LieBtrau/garage-door-rke/hardware/testReports/measurementResults/BRD220522_2/4.1Vin_default_tx_power.png

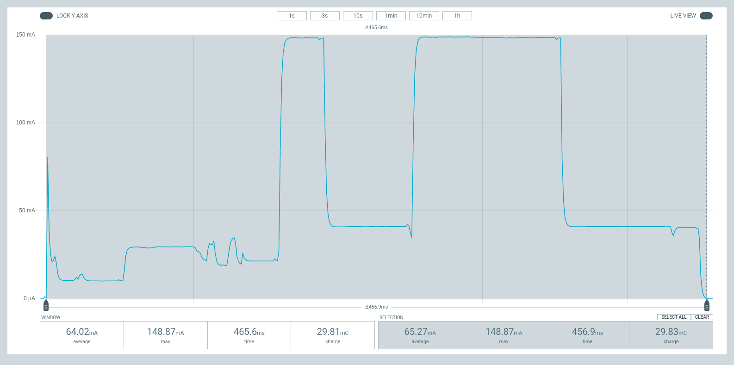
hardware/testReports/measurementResults/BRD220522_2/4.1Vin_default_tx_power.png
