LieBtrau/garage-door-rke/hardware/testReports/measurementResults/BRD220522_2/SPI/IMG_20221129_220042_032.jpg

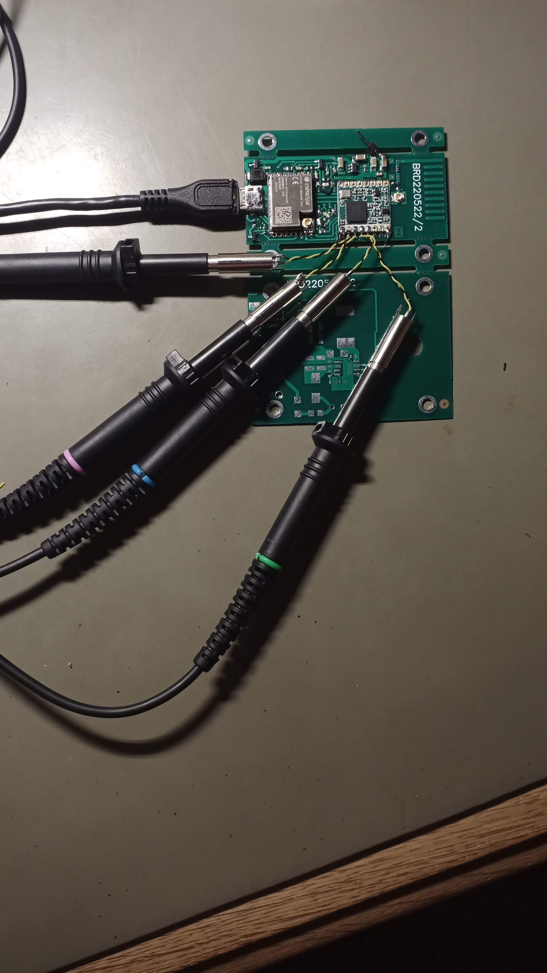
hardware/testReports/measurementResults/BRD220522_2/SPI/IMG_20221129_220042_032.jpg
