LieBtrau/garage-door-rke/hardware/testReports/measurementResults/BRD220522_2/SPI/MISO_timing.png

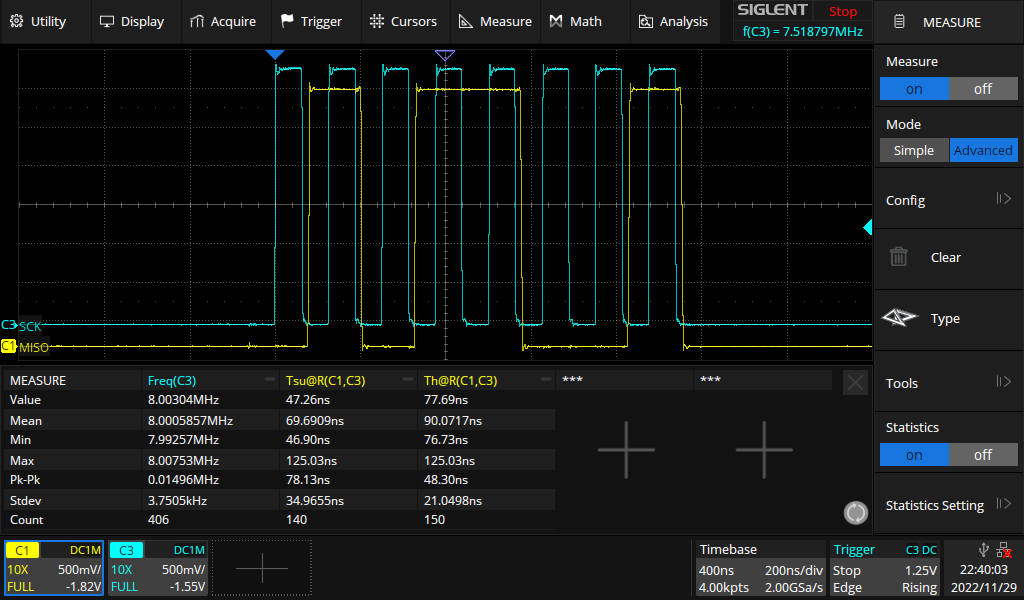
hardware/testReports/measurementResults/BRD220522_2/SPI/MISO_timing.png
