LieBtrau/garage-door-rke/hardware/testReports/measurementResults/BRD220522_2/SPI/MOSI.png

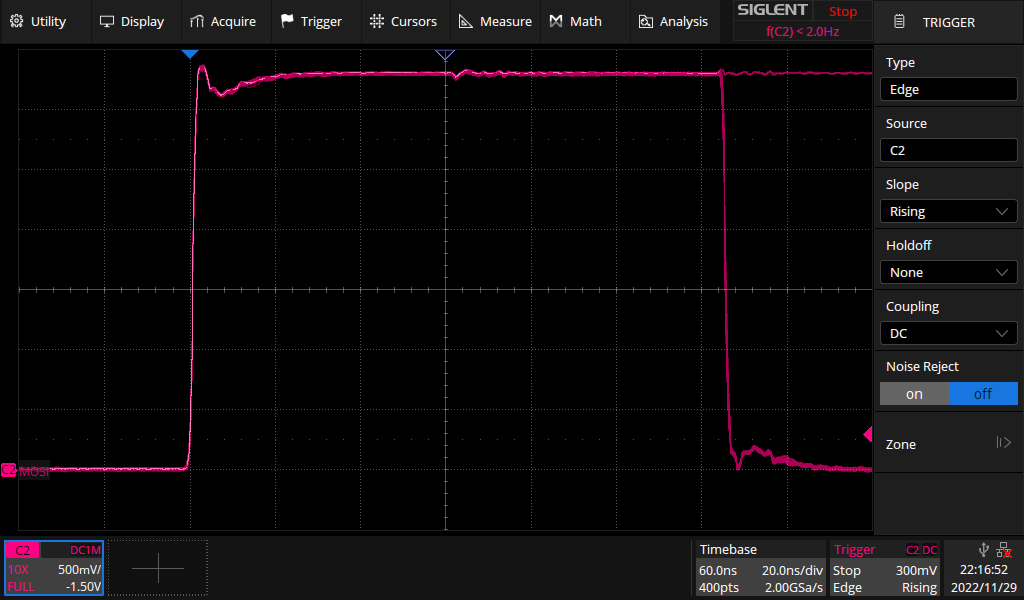
hardware/testReports/measurementResults/BRD220522_2/SPI/MOSI.png
