LieBtrau/garage-door-rke/hardware/testReports/measurementResults/BRD220522_2/SPI/nCS_fallingEdge.png

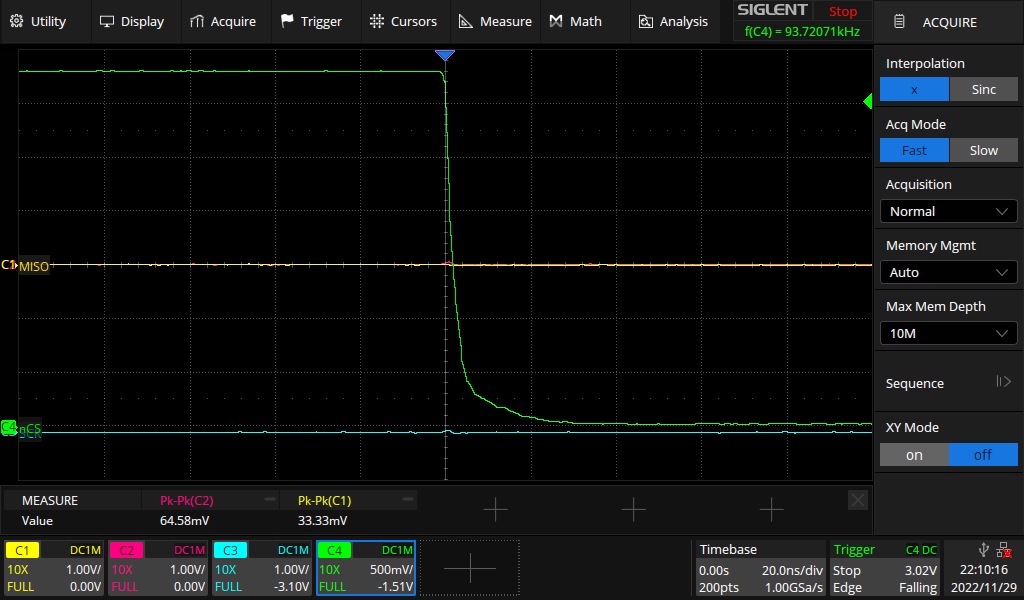
hardware/testReports/measurementResults/BRD220522_2/SPI/nCS_fallingEdge.png
