LieBtrau/garage-door-rke/hardware/testReports/measurementResults/BRD220522_2/SPI/SCK.png

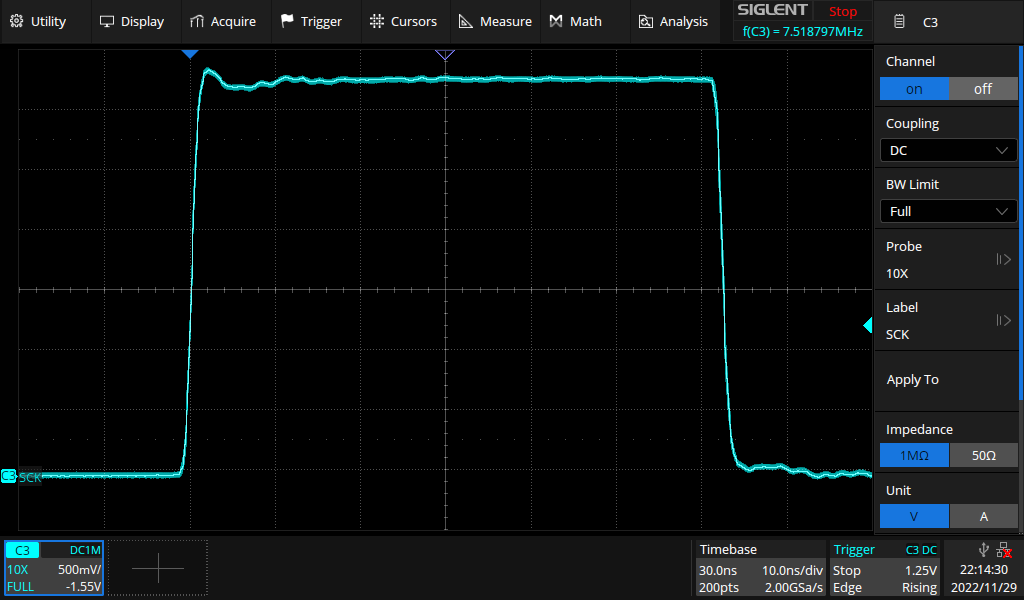
hardware/testReports/measurementResults/BRD220522_2/SPI/SCK.png
