LieBtrau/garage-door-rke/hardware/testReports/measurementResults/BRD220523_1/5V_rampUp.png

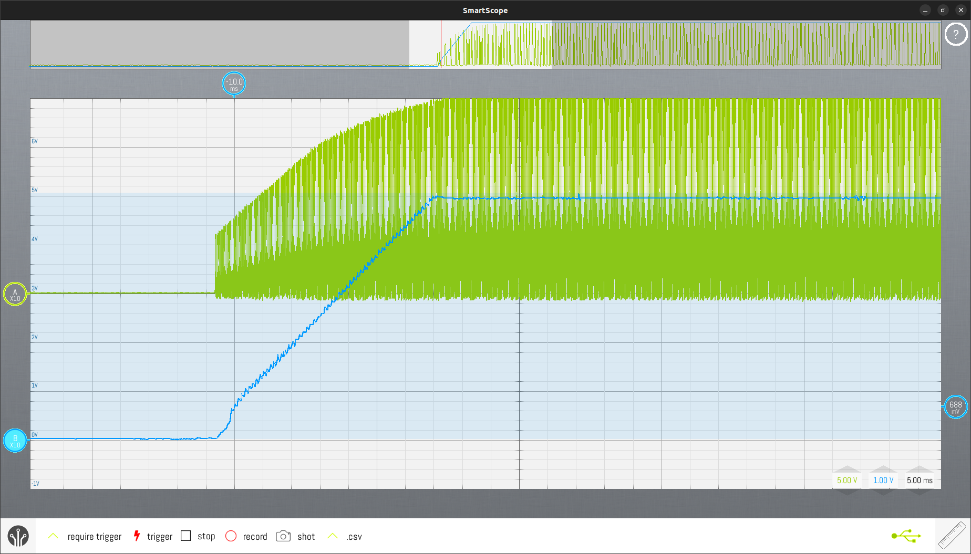
hardware/testReports/measurementResults/BRD220523_1/5V_rampUp.png
