LieBtrau/garage-door-rke/hardware/testReports/measurementResults/BRD220523_1/10Vin_1Aout.png

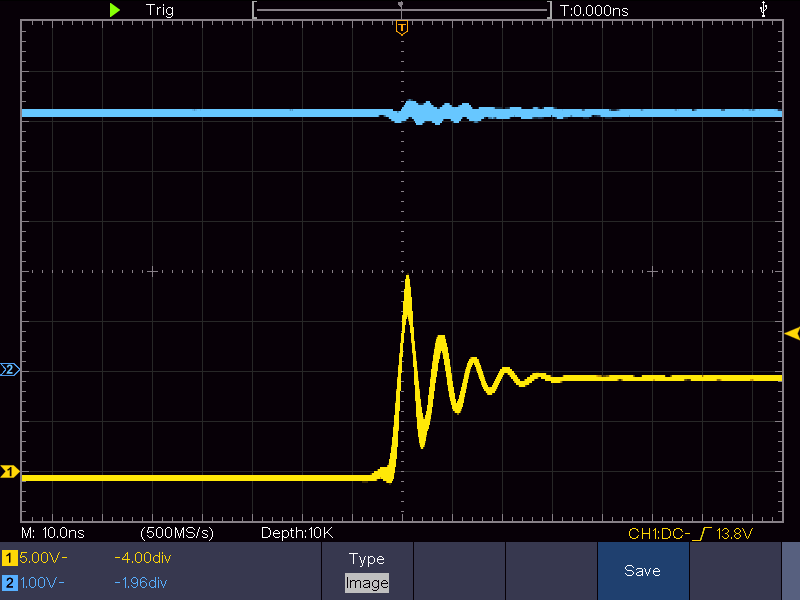
hardware/testReports/measurementResults/BRD220523_1/10Vin_1Aout.png
