LieBtrau/garage-door-rke/hardware/testReports/measurementResults/BRD220523_2/input_voltage_ripple.png

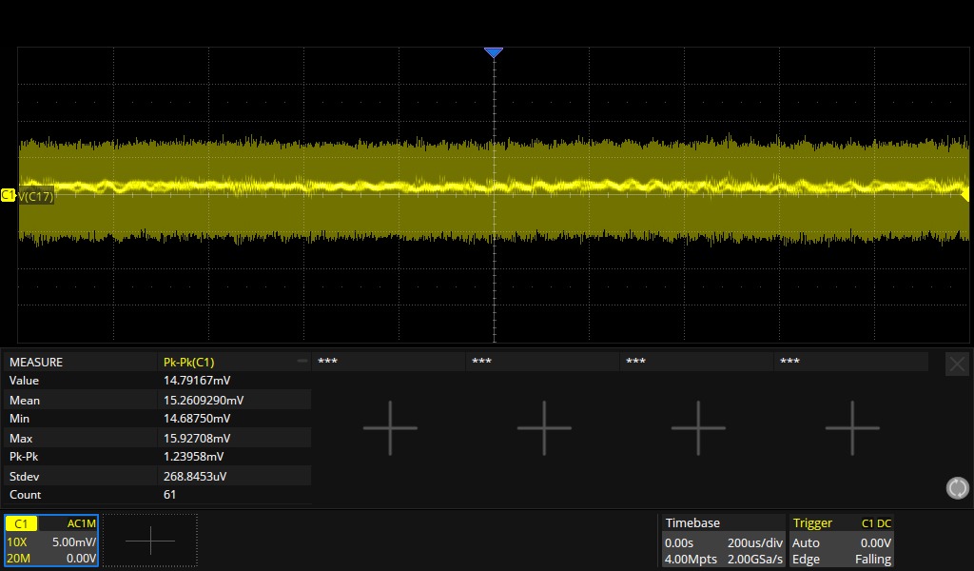
hardware/testReports/measurementResults/BRD220523_2/input_voltage_ripple.png
