LieBtrau/garage-door-rke/hardware/testReports/measurementResults/BRD220523_2/switching_node_frequency_B350A.png

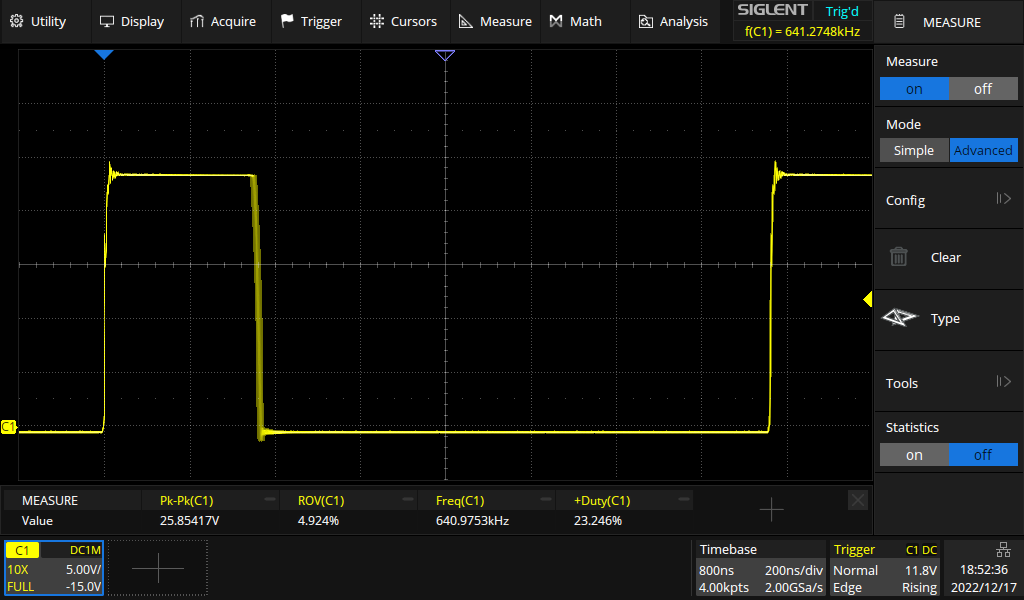
hardware/testReports/measurementResults/BRD220523_2/switching_node_frequency_B350A.png
