LieBtrau/garage-door-rke/hardware/testReports/measurementResults/BRD220523_2/vin_rising_1.png

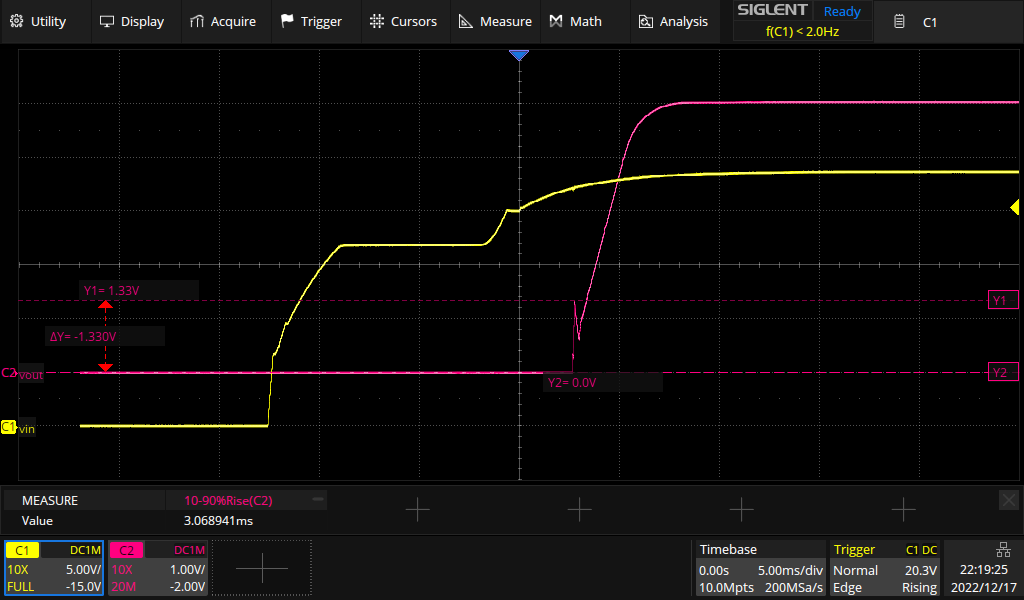
hardware/testReports/measurementResults/BRD220523_2/vin_rising_1.png
