LieBtrau/garage-door-rke/hardware/testReports/measurementResults/BRD220523_2/vin_rising_C10.png

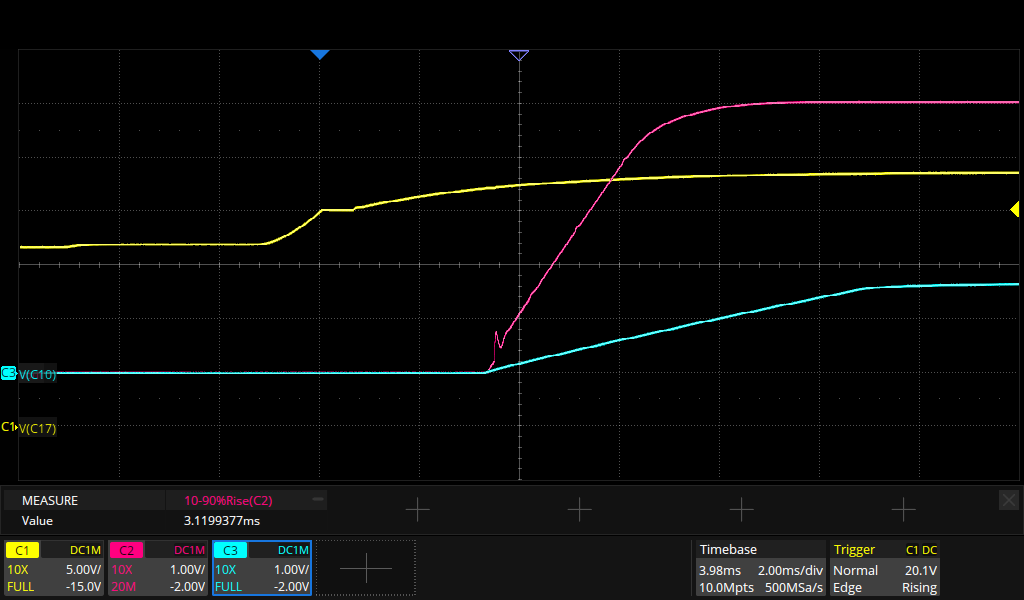
hardware/testReports/measurementResults/BRD220523_2/vin_rising_C10.png
