LieBtrau/garage-door-rke/hardware/testReports/measurementResults/BRD220523_2/vout_falling.png

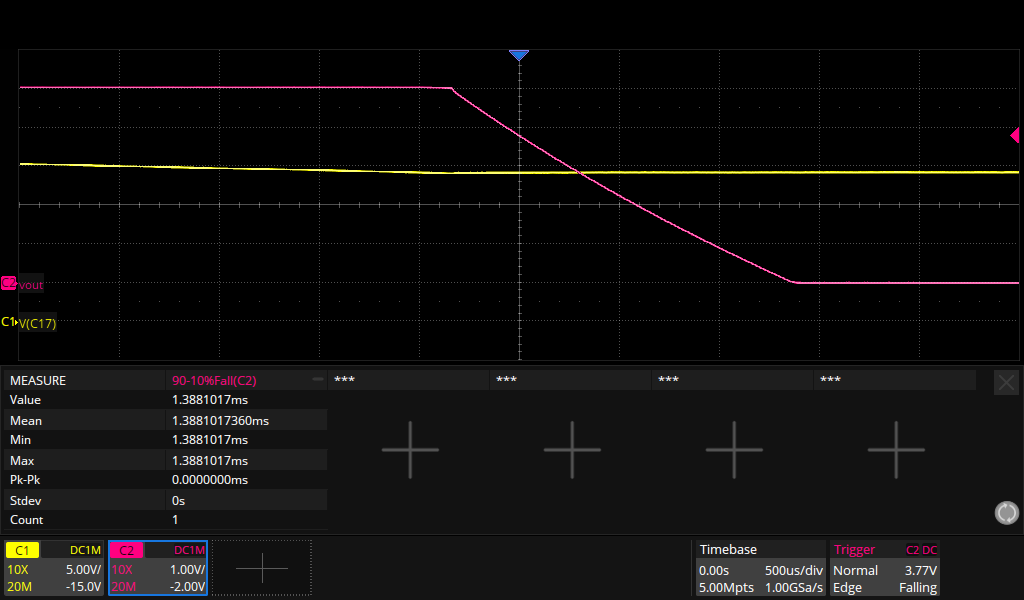
hardware/testReports/measurementResults/BRD220523_2/vout_falling.png
