LieBtrau/garage-door-rke/firmware/garage-door-rke/src/webserver.cpp

/** \file brd220522_webserver
 * 
 * \author Christoph Tack
 * \date 2022-12-24
 * \brief Webserver for access control with pin code
 * \details When browsing to the webserver, pin_form.html is served to the client.  The client fills in the pin code and generates
 * a HTTP-POST message.  The server checks the pin code and send a dynamically generated webpage (door.html) back to the client.
 */

#if REMOTE == 0   //only the garage door controller has a web interface

#include "WiFi.h"
#include "ESPAsyncWebServer.h"
#include "SPIFFS.h"
#include "wifi_credentials.h"
#include "constants.h"

static const char* TAG = "WebServer";

static bool isAccessGranted=false;
static AsyncWebServer server(80);  // server on port 80

/**
 * @brief Replace placeholder with the desired string
 * 
 * @param var placeholder string to be replaced
 * @return String 
 */
static String processor(const String &var)
{
  if (var == "DOOR_STATE")
  {
    return isAccessGranted ? "open" : "blijft gesloten";
  }
  return String();
}

/**
 * @brief Parse HTTP-POST message
 * Iterate over the posted parameters.  Check if the pin code is correct.  Send back an appropriate HTML-page.
 * @param request 
 */
static void action(AsyncWebServerRequest *request)
{
  isAccessGranted = false;
  int params = request->params();
  for (int i = 0; i < params; i++)
  {
    AsyncWebParameter *p = request->getParam(i);
    if (p->name() == "pincode" && p->value() == PIN_CODE)
    {
      isAccessGranted = true;
    }
  }
  request->send(SPIFFS, "/door.html", String(), false, processor);
  if(isAccessGranted)
  {
    authenticationOkAction();
  }
  isAccessGranted = false;
}

bool webserver_setup()
{
  Serial.begin(115200);
  if (!SPIFFS.begin(true))
  {
    ESP_LOGE(TAG, "An Error has occurred while mounting SPIFFS");
    return false;
  }
  // Configures static IP address
  IPAddress local_IP(192, 168, 1, 253); // Set your Static IP address
  IPAddress gateway(192, 168, 1, 1);    // Set your Gateway IP address
  IPAddress subnet(255, 255, 255, 0);
  if (!WiFi.config(local_IP, gateway, subnet))
  {
    ESP_LOGE(TAG, "STA Failed to configure");
    return false;
  }
  WiFi.begin(SSID, PASSWORD);
  while (WiFi.status() != WL_CONNECTED)
  {
    delay(1000);
    ESP_LOGD(TAG, "Connecting to WiFi..");
  }
  // Route for root / web page
  server.on("/", HTTP_GET, [](AsyncWebServerRequest *request)
            { request->send(SPIFFS, "/pin_form.html", String(), false); });

  server.on("/login", HTTP_POST, action);
  server.begin();
  return true;
}

#endif
