LieBtrau/garage-door-rke/firmware/tests/webserver-authentication/src/main.cpp

// https://randomnerdtutorials.com/esp32-esp8266-web-server-http-authentication/
/*********
  Rui Santos
  Complete project details at https://RandomNerdTutorials.com/esp32-esp8266-web-server-http-authentication/

  The above copyright notice and this permission notice shall be included in all
  copies or substantial portions of the Software.
*********/

// Import required libraries
#include <WiFi.h>
#include <AsyncTCP.h>
#include <ESPAsyncWebServer.h>

// Replace with your network credentials
#include "wifi_cred.h"

const char *http_username = "admin";
const char *http_password = "admin";

const char *PARAM_INPUT_1 = "state";

const int output = 3;

// Create AsyncWebServer object on port 80
AsyncWebServer server(80);

const char index_html[] PROGMEM = R"rawliteral(
<!DOCTYPE HTML><html>
<head>
  <title>ESP Web Server</title>
  <meta name="viewport" content="width=device-width, initial-scale=1">
  <style>
    html {font-family: Arial; display: inline-block; text-align: center;}
    h2 {font-size: 2.6rem;}
    body {max-width: 600px; margin:0px auto; padding-bottom: 10px;}
    .switch {position: relative; display: inline-block; width: 120px; height: 68px} 
    .switch input {display: none}
    .slider {position: absolute; top: 0; left: 0; right: 0; bottom: 0; background-color: #ccc; border-radius: 34px}
    .slider:before {position: absolute; content: ""; height: 52px; width: 52px; left: 8px; bottom: 8px; background-color: #fff; -webkit-transition: .4s; transition: .4s; border-radius: 68px}
    input:checked+.slider {background-color: #2196F3}
    input:checked+.slider:before {-webkit-transform: translateX(52px); -ms-transform: translateX(52px); transform: translateX(52px)}
  </style>
</head>
<body>
  <h2>ESP Web Server</h2>
  <button onclick="logoutButton()">Logout</button>
  <p>Ouput - GPIO 2 - State <span id="state">%STATE%</span></p>
  %BUTTONPLACEHOLDER%
<script>function toggleCheckbox(element) {
  var xhr = new XMLHttpRequest();
  if(element.checked){ 
    xhr.open("GET", "/update?state=1", true); 
    document.getElementById("state").innerHTML = "ON";  
  }
  else { 
    xhr.open("GET", "/update?state=0", true); 
    document.getElementById("state").innerHTML = "OFF";      
  }
  xhr.send();
}
function logoutButton() {
  var xhr = new XMLHttpRequest();
  xhr.open("GET", "/logout", true);
  xhr.send();
  setTimeout(function(){ window.open("/logged-out","_self"); }, 1000);
}
</script>
</body>
</html>
)rawliteral";

const char logout_html[] PROGMEM = R"rawliteral(
<!DOCTYPE HTML><html>
<head>
  <meta name="viewport" content="width=device-width, initial-scale=1">
</head>
<body>
  <p>Logged out or <a href="/">return to homepage</a>.</p>
  <p><strong>Note:</strong> close all web browser tabs to complete the logout process.</p>
</body>
</html>
)rawliteral";

String outputState()
{
	if (digitalRead(output))
	{
		return "checked";
	}
	else
	{
		return "";
	}
	return "";
}


// Replaces placeholder with button section in your web page
String processor(const String &var)
{
	// Serial.println(var);
	if (var == "BUTTONPLACEHOLDER")
	{
		String buttons = "";
		String outputStateValue = outputState();
		buttons += "<p><label class=\"switch\"><input type=\"checkbox\" onchange=\"toggleCheckbox(this)\" id=\"output\" " + outputStateValue + "><span class=\"slider\"></span></label></p>";
		return buttons;
	}
	if (var == "STATE")
	{
		if (digitalRead(output))
		{
			return "ON";
		}
		else
		{
			return "OFF";
		}
	}
	return String();
}

void setup()
{
	// Serial port for debugging purposes
	Serial.begin(115200);

	pinMode(output, OUTPUT);
	digitalWrite(output, LOW);

	Serial.println("Start");

	//Static IP-configuration (leave away when dynamic IP config is desired)
	IPAddress local_IP(192, 168, 1, 253);
	IPAddress gateway(192, 168, 1, 1);
	IPAddress subnet(255, 255, 255, 0);
	if (!WiFi.config(local_IP, gateway, subnet))
	{
		Serial.println("STA Failed to configure");
	}

	// Connect to Wi-Fi
	WiFi.begin(ssid, password);
	while (WiFi.status() != WL_CONNECTED)
	{
		delay(1000);
		Serial.println("Connecting to WiFi..");
	}

	// Print ESP Local IP Address
	Serial.println(WiFi.localIP());

	// Route for root / web page
	server.on("/", HTTP_GET, [](AsyncWebServerRequest *request)
			  {
    if(!request->authenticate(http_username, http_password))
      return request->requestAuthentication();
    request->send_P(200, "text/html", index_html, processor); });

	server.on("/logout", HTTP_GET, [](AsyncWebServerRequest *request)
			  { request->send(401); });

	server.on("/logged-out", HTTP_GET, [](AsyncWebServerRequest *request)
			  { request->send_P(200, "text/html", logout_html, processor); });

	// Send a GET request to <ESP_IP>/update?state=<inputMessage>
	server.on("/update", HTTP_GET, [](AsyncWebServerRequest *request)
			  {
    if(!request->authenticate(http_username, http_password))
      return request->requestAuthentication();
    String inputMessage;
    String inputParam;
    // GET input1 value on <ESP_IP>/update?state=<inputMessage>
    if (request->hasParam(PARAM_INPUT_1)) {
      inputMessage = request->getParam(PARAM_INPUT_1)->value();
      inputParam = PARAM_INPUT_1;
      digitalWrite(output, inputMessage.toInt());
    }
    else {
      inputMessage = "No message sent";
      inputParam = "none";
    }
    Serial.println(inputMessage);
    request->send(200, "text/plain", "OK"); });

	// Start server
	server.begin();
}

void loop()
{
}
