LieBtrau/garage-door-rke/firmware/tests/brd220522_2_Blinky/src/main.cpp

#include <Arduino.h>

const int led_green = 8;
const int led_red = 4;

void setup() {
  // put your setup code here, to run once:
  pinMode(led_green, OUTPUT);
  pinMode(led_red, OUTPUT);
}

void loop() {
  // put your main code here, to run repeatedly:
  digitalWrite(led_green, HIGH);
  digitalWrite(led_red, LOW);
  delay(500);
  digitalWrite(led_green, LOW);
  digitalWrite(led_red, HIGH);
  delay(500);
}
