LieBtrau/garage-door-rke/firmware/tests/webserver-spiffs/src/main.cpp

/*********
  Rui Santos
  Complete project details at https://randomnerdtutorials.com
  https://randomnerdtutorials.com/esp32-web-server-spiffs-spi-flash-file-system/
  https://randomnerdtutorials.com/esp32-vs-code-platformio-spiffs/

  Lolin-C3 doesn't connect to WiFi.  Possible causes : LDO too weak, not enough bulk cap.

*********/

// Import required libraries
#include "WiFi.h"
#include "ESPAsyncWebServer.h"
#include "SPIFFS.h"

// Replace with your network credentials
#include "wifi_cred.h"

// Set LED GPIO
const int ledPin = 3;
// Stores LED state
String ledState;

// Create AsyncWebServer object on port 80
AsyncWebServer server(80);

// Replaces placeholder with LED state value
String processor(const String &var)
{
	Serial.println(var);
	if (var == "STATE")
	{
		if (digitalRead(ledPin))
		{
			ledState = "ON";
		}
		else
		{
			ledState = "OFF";
		}
		Serial.print(ledState);
		return ledState;
	}
	return String();
}

void setup()
{
	// Serial port for debugging purposes
	Serial.begin(115200);
	pinMode(ledPin, OUTPUT);

	// Initialize SPIFFS
	if (!SPIFFS.begin(true))
	{
		Serial.println("An Error has occurred while mounting SPIFFS");
		return;
	}

	//Static IP-configuration (leave away when dynamic IP config is desired)
	IPAddress local_IP(192, 168, 1, 253);
	IPAddress gateway(192, 168, 1, 1);
	IPAddress subnet(255, 255, 255, 0);
	if (!WiFi.config(local_IP, gateway, subnet))
	{
		Serial.println("STA Failed to configure");
	}

	// Connect to Wi-Fi
	WiFi.begin(ssid, password);
	while (WiFi.status() != WL_CONNECTED)
	{
		delay(1000);
		Serial.println("Connecting to WiFi..");
	}

	// Print ESP32 Local IP Address
	Serial.println(WiFi.localIP());

	// Route for root / web page
	server.on("/", HTTP_GET, [](AsyncWebServerRequest *request)
			  { request->send(SPIFFS, "/index.html", String(), false, processor); });

	// Route to load style.css file
	server.on("/style.css", HTTP_GET, [](AsyncWebServerRequest *request)
			  { request->send(SPIFFS, "/style.css", "text/css"); });

	// Route to set GPIO to HIGH
	server.on("/on", HTTP_GET, [](AsyncWebServerRequest *request)
			  {
    digitalWrite(ledPin, HIGH);    
    request->send(SPIFFS, "/index.html", String(), false, processor); });

	// Route to set GPIO to LOW
	server.on("/off", HTTP_GET, [](AsyncWebServerRequest *request)
			  {
    digitalWrite(ledPin, LOW);    
    request->send(SPIFFS, "/index.html", String(), false, processor); });

	// Start server
	server.begin();
}

void loop()
{
}
